MarcFinns/ESP-P1-Meter/Pictures/2.jpeg

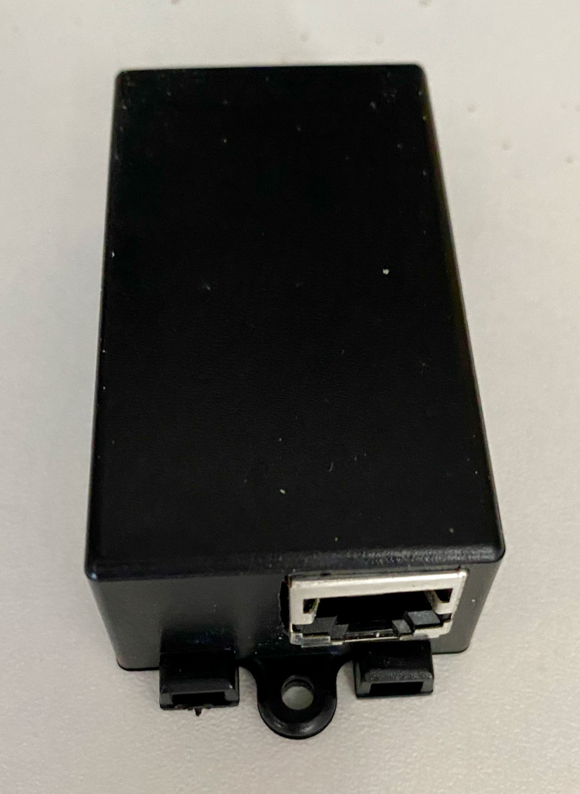
Pictures/2.jpeg
