MarcFinns/ESP-P1-Meter/Pictures/4.jpeg

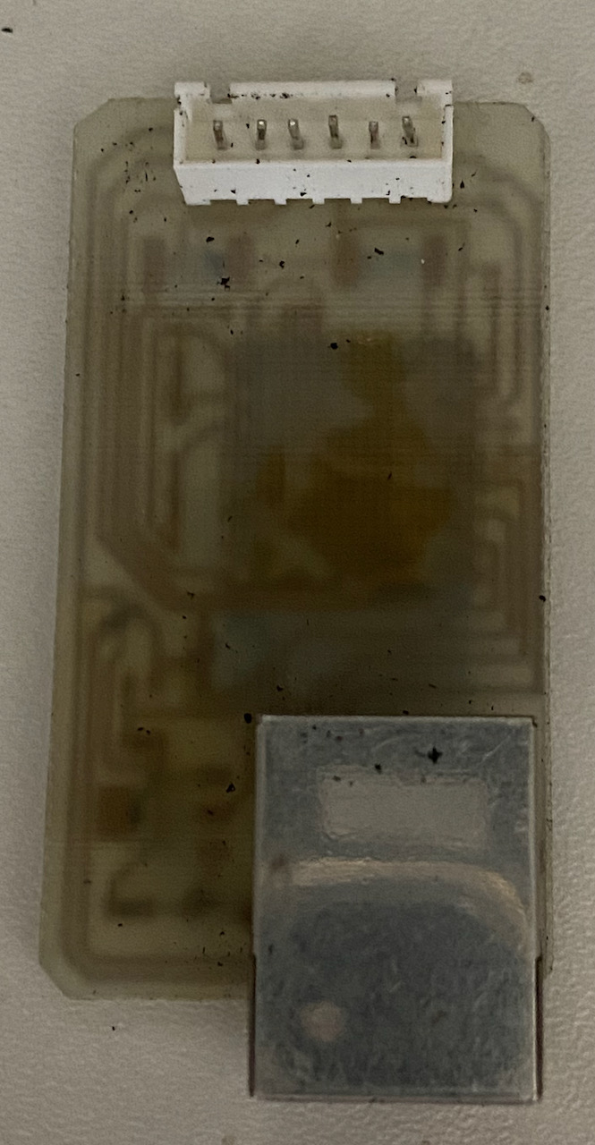
Pictures/4.jpeg
