MarcFinns/ESP-P1-Meter/Pictures/5.jpeg

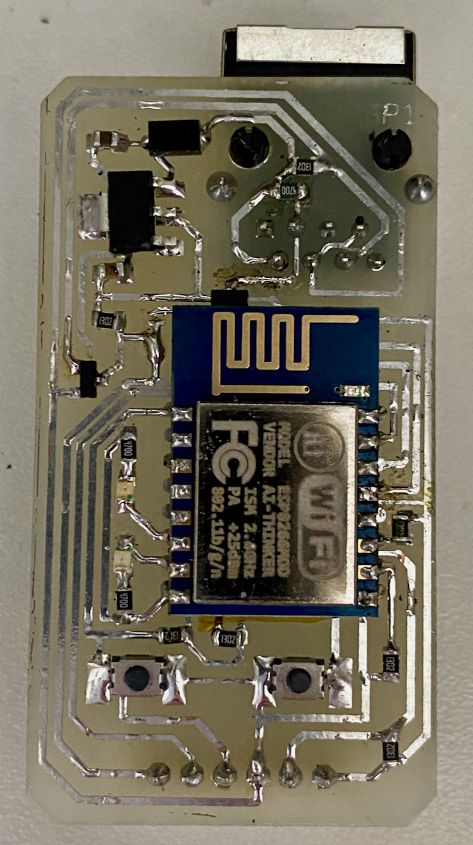
Pictures/5.jpeg
